JakubKivi/K-Pillar/src/hardware/Pump.cpp

#include "Pump.h"

// #define IS_DEV  

Pump::Pump(int pin, int id) : pin(pin), state(false), id(id) {
    pinMode(pin, OUTPUT);
    digitalWrite(pin, LOW);
}

void Pump::setState(bool newState) {
    state = newState; // Stan zawsze się aktualizuje

#ifndef IS_DEV
    digitalWrite(pin, state ? HIGH : LOW);
#endif
}

bool Pump::getState() {
    return state;
}
